chipdipru/RDC1-0034.-Fully-Differential-amp./pic0034/RDC1-0034_sch.png

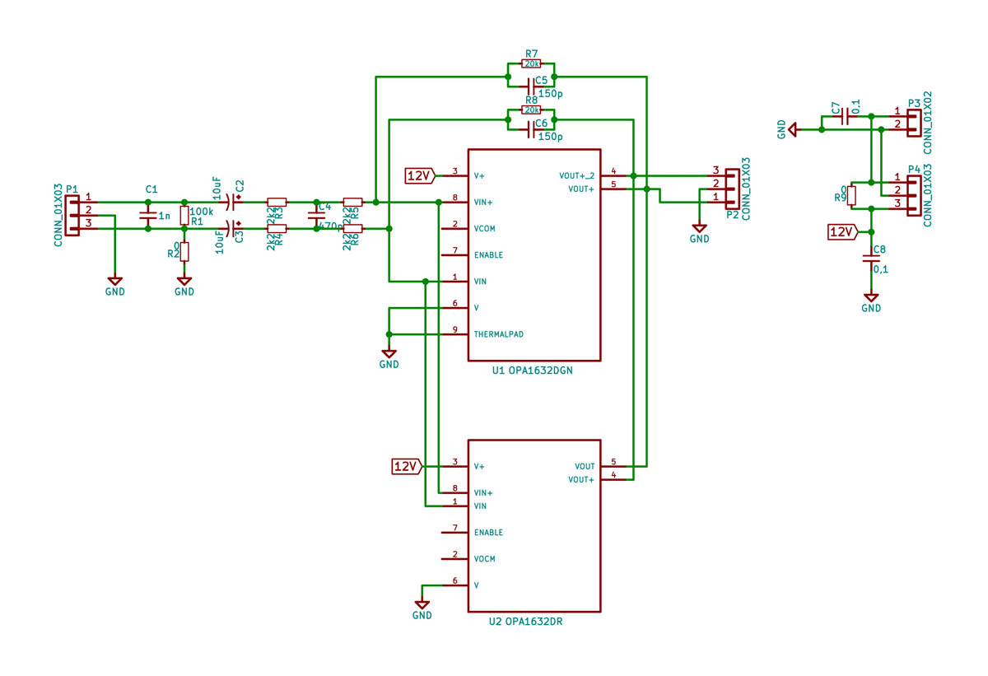
pic0034/RDC1-0034_sch.png
